taskx6004/ulx4m/pic/shipping.png

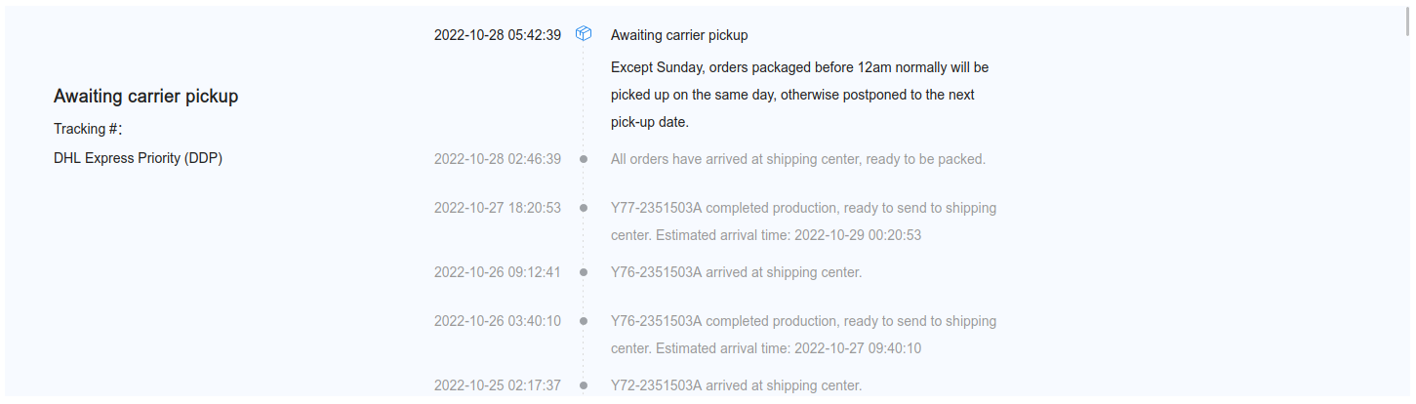
pic/shipping.png
