taskx6004/ulx4m/pic/ULX4M-LD_bottom_v001.png

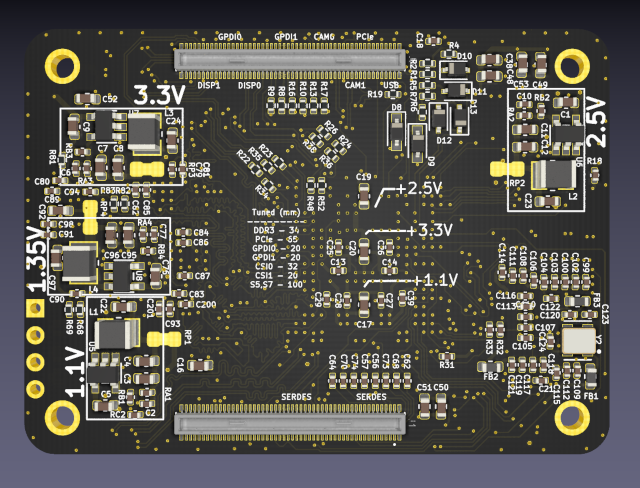
pic/ULX4M-LD_bottom_v001.png
