taskx6004/ulx4m/pic/ulx4m.png

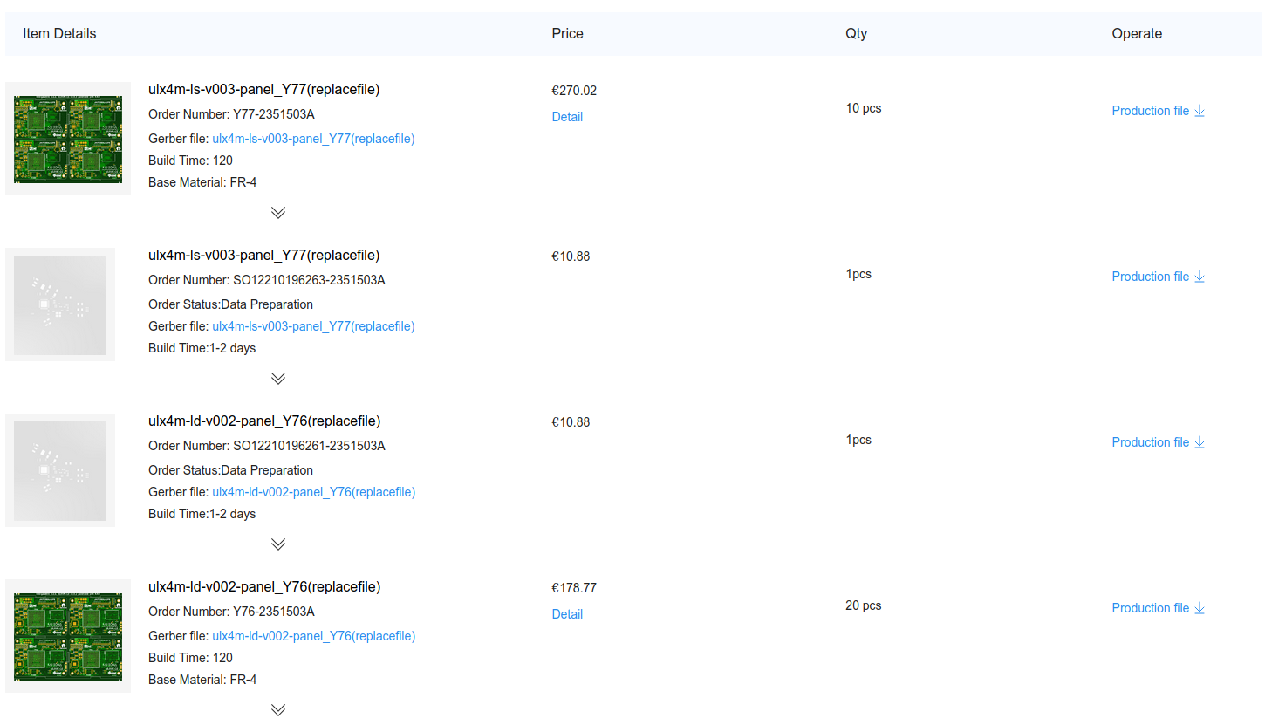
pic/ulx4m.png
