taskx6004/ulx4m/pic/ULX4M_bottom_v002.png

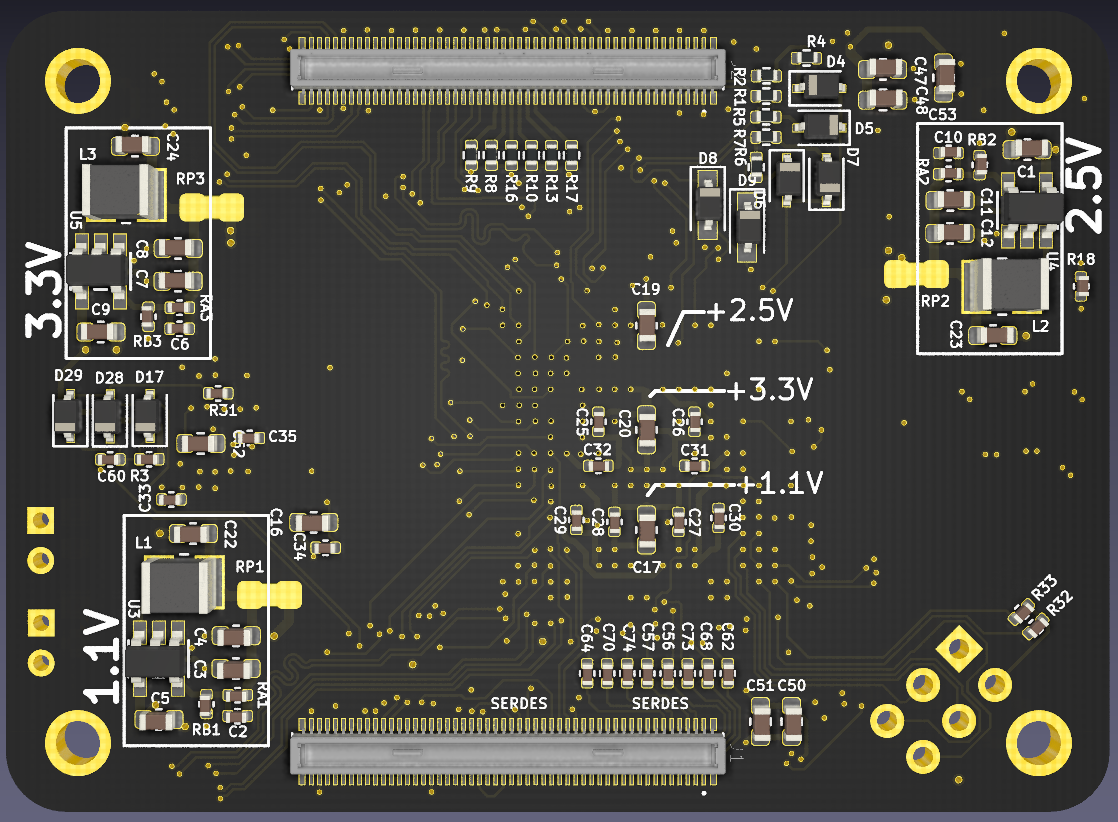
pic/ULX4M_bottom_v002.png
