taskx6004/ulx4m/pic/ulx4m_ld_panel.png

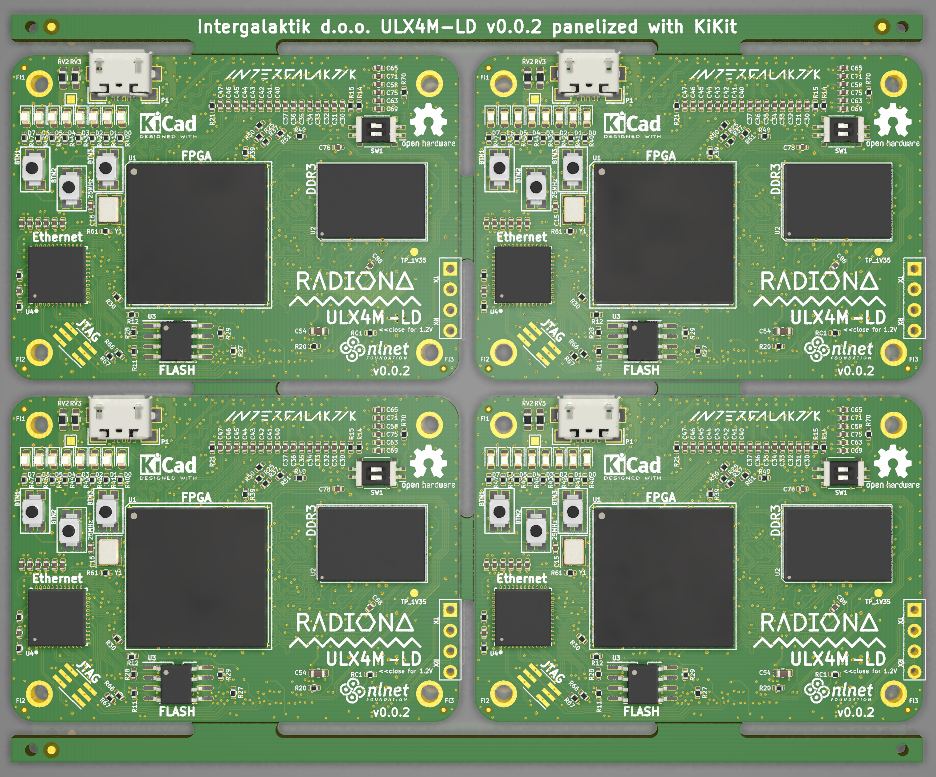
pic/ulx4m_ld_panel.png
