taskx6004/ulx4m/pic/ULX4M_routed_V002.png

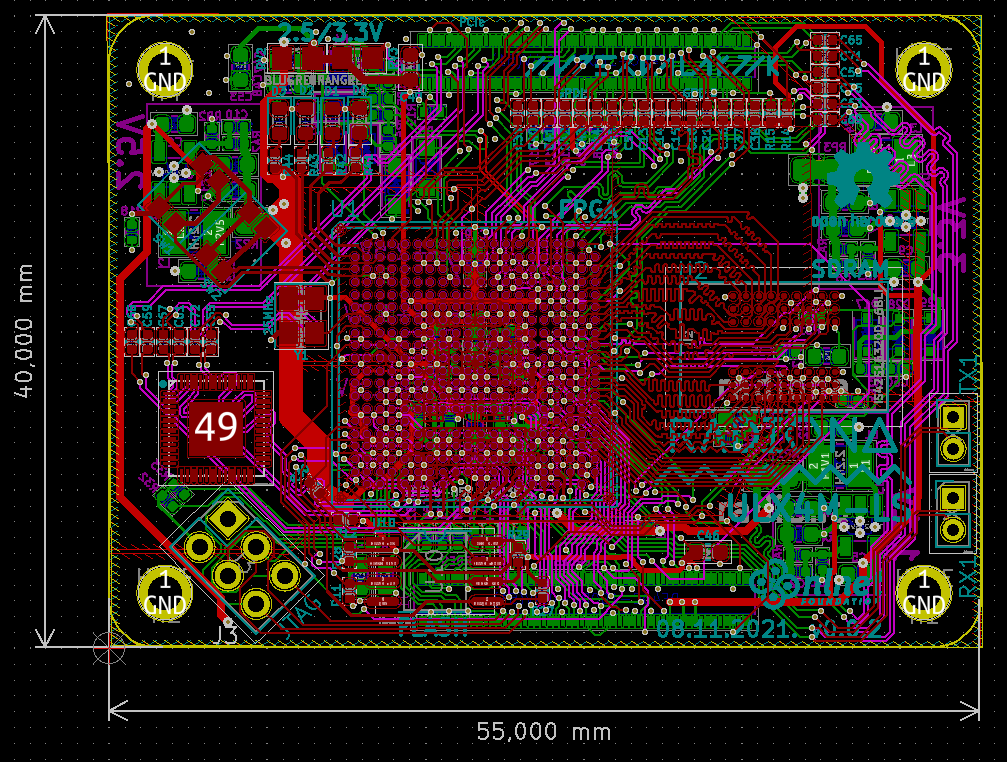
pic/ULX4M_routed_V002.png
